dansity/vibration_mole_repellent/img/IMG_20240617_125319968.jpg

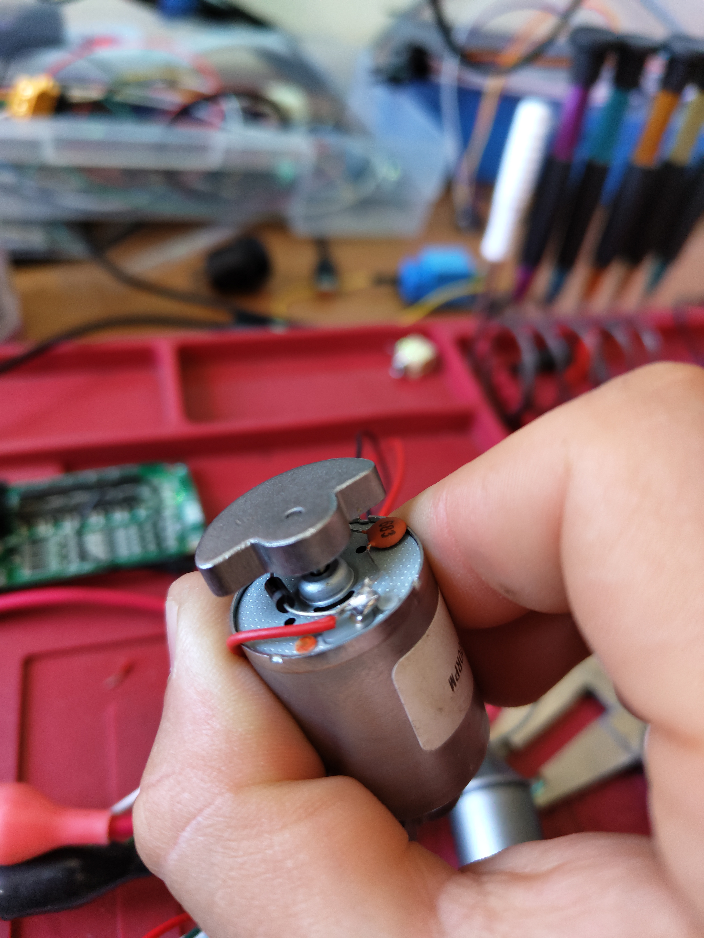
img/IMG_20240617_125319968.jpg
