dansity/vibration_mole_repellent/img/IMG_20240617_173355589.jpg

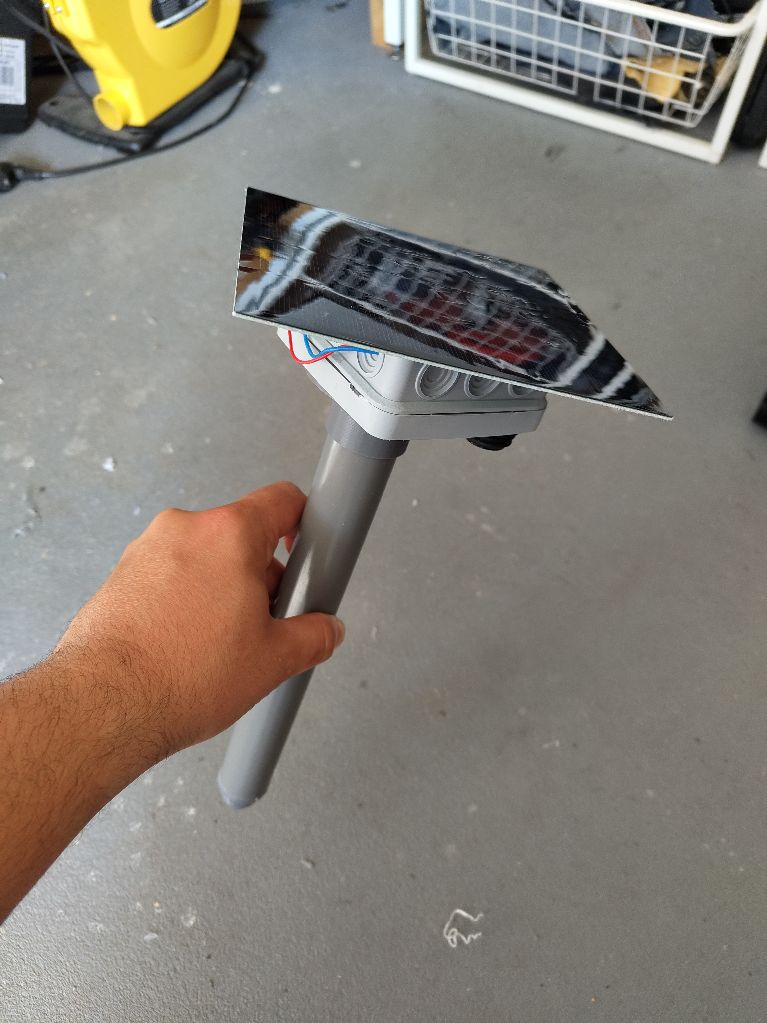
img/IMG_20240617_173355589.jpg
